cerevo/MKZ4/custom/milkcocoa_javascript/image/b_right.png

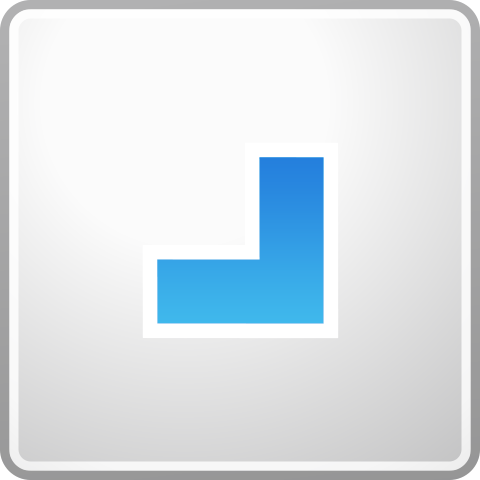
custom/milkcocoa_javascript/image/b_right.png
