cerevo/MKZ4/custom/MKZ4Camera/Pics/Front.jpg

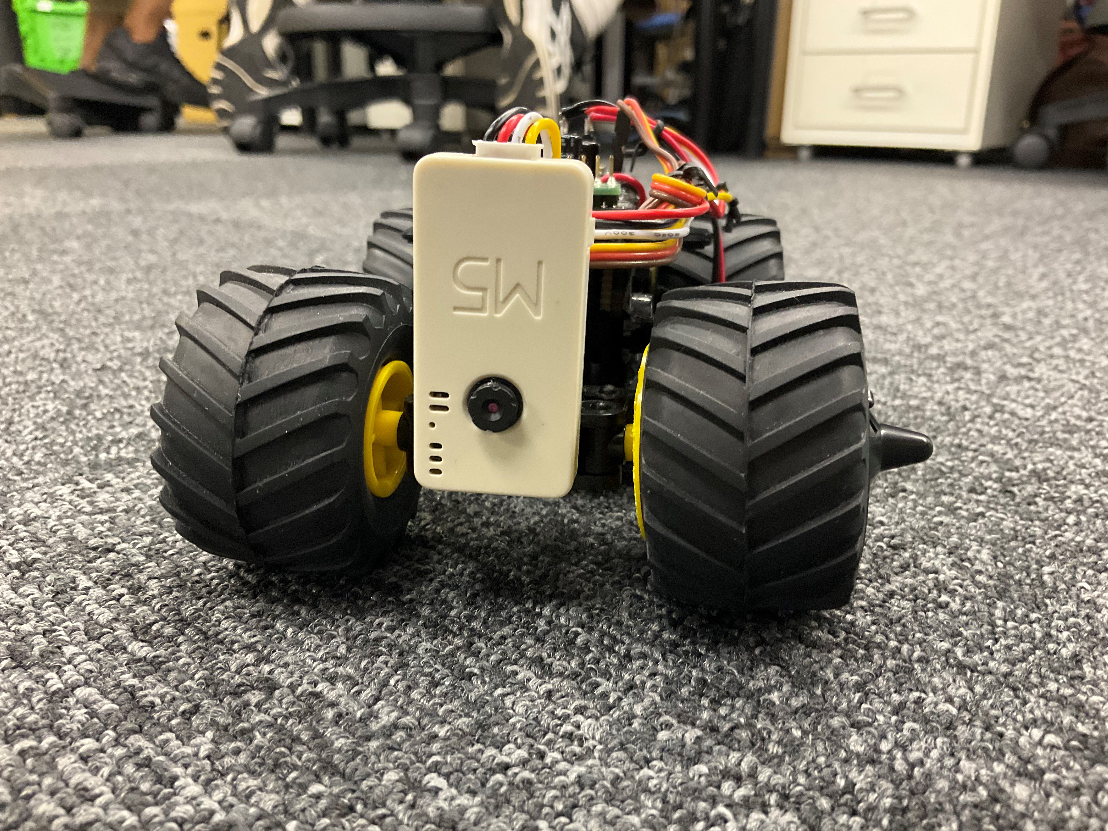
custom/MKZ4Camera/Pics/Front.jpg
