cerevo/MKZ4/custom/MKZ4Camera/CameraWebserver/app_httpd.cpp

// Copyright 2015-2016 Espressif Systems (Shanghai) PTE LTD
//
// Licensed under the Apache License, Version 2.0 (the "License");
// you may not use this file except in compliance with the License.
// You may obtain a copy of the License at
//
//     http://www.apache.org/licenses/LICENSE-2.0
//
// Unless required by applicable law or agreed to in writing, software
// distributed under the License is distributed on an "AS IS" BASIS,
// WITHOUT WARRANTIES OR CONDITIONS OF ANY KIND, either express or implied.
// See the License for the specific language governing permissions and
// limitations under the License.
#include "esp_http_server.h"
#include "esp_timer.h"
#include "esp_camera.h"
#include "img_converters.h"
#include "fb_gfx.h"
#include "driver/ledc.h"
#include "sdkconfig.h"
#include "camera_index.h"

#include "Arduino.h"

#if defined(ARDUINO_ARCH_ESP32) && defined(CONFIG_ARDUHAL_ESP_LOG)
#include "esp32-hal-log.h"
#define TAG "WS"
#else
#include "esp_log.h"
static const char *TAG = "camera_httpd";
#endif

typedef struct
{
    httpd_req_t *req;
    size_t len;
} jpg_chunking_t;

/*
 * Structure holding server handle
 * and internal socket fd in order
 * to use out of request send
 */
struct async_resp_arg
{
    httpd_handle_t hd;
    int fd;
};

#define PART_BOUNDARY "123456789000000000000987654321"
static const char *_STREAM_CONTENT_TYPE = "multipart/x-mixed-replace;boundary=" PART_BOUNDARY;
static const char *_STREAM_BOUNDARY = "\r\n--" PART_BOUNDARY "\r\n";
static const char *_STREAM_PART = "Content-Type: image/jpeg\r\nContent-Length: %u\r\nX-Timestamp: %d.%06d\r\n\r\n";

httpd_handle_t stream_httpd = NULL;
httpd_handle_t camera_httpd = NULL;

typedef struct
{
    size_t size;  //number of values used for filtering
    size_t index; //current value index
    size_t count; //value count
    int sum;
    int *values; //array to be filled with values
} ra_filter_t;

static ra_filter_t ra_filter;

static ra_filter_t *ra_filter_init(ra_filter_t *filter, size_t sample_size)
{
    memset(filter, 0, sizeof(ra_filter_t));

    filter->values = (int *)malloc(sample_size * sizeof(int));
    if (!filter->values)
    {
        return NULL;
    }
    memset(filter->values, 0, sample_size * sizeof(int));

    filter->size = sample_size;
    return filter;
}


///////////////////////////////////////////////////////////////////////////////////////////////////

/*
 * async send function, which we put into the httpd work queue
 */
static void ws_async_send(void *arg)
{
    static const char *data = "Async data";
    struct async_resp_arg *resp_arg = (struct async_resp_arg*)arg;
    httpd_handle_t hd = resp_arg->hd;
    int fd = resp_arg->fd;
    httpd_ws_frame_t ws_pkt;
    memset(&ws_pkt, 0, sizeof(httpd_ws_frame_t));
    ws_pkt.payload = (uint8_t *)data;
    ws_pkt.len = strlen(data);
    ws_pkt.type = HTTPD_WS_TYPE_TEXT;

    httpd_ws_send_frame_async(hd, fd, &ws_pkt);
    free(resp_arg);
}

static esp_err_t trigger_async_send(httpd_handle_t handle, httpd_req_t *req)
{
    struct async_resp_arg *resp_arg = (struct async_resp_arg *)malloc(sizeof(struct async_resp_arg));
    resp_arg->hd = req->handle;
    resp_arg->fd = httpd_req_to_sockfd(req);
    return httpd_queue_work(handle, ws_async_send, resp_arg);
}

/*
 * This handler echos back the received ws data
 * and triggers an async send if certain message received
 */
static esp_err_t echo_handler(httpd_req_t *req)
{
    if (req->method == HTTP_GET)
    {
        ESP_LOGI(TAG, "Handshake done, the new connection was opened");
        return ESP_OK;
    }
    httpd_ws_frame_t ws_pkt;
    uint8_t *buf = NULL;
    memset(&ws_pkt, 0, sizeof(httpd_ws_frame_t));
    ws_pkt.type = HTTPD_WS_TYPE_TEXT;
    /* Set max_len = 0 to get the frame len */
    esp_err_t ret = httpd_ws_recv_frame(req, &ws_pkt, 0);
    if (ret != ESP_OK)
    {
        ESP_LOGE(TAG, "httpd_ws_recv_frame failed to get frame len with %d", ret);
        return ret;
    }
    ESP_LOGI(TAG, "frame len is %d", ws_pkt.len);
    if (ws_pkt.len)
    {
        /* ws_pkt.len + 1 is for NULL termination as we are expecting a string */
        buf = (uint8_t*)calloc(1, ws_pkt.len + 1);
        if (buf == NULL)
        {
            ESP_LOGE(TAG, "Failed to calloc memory for buf");
            return ESP_ERR_NO_MEM;
        }
        ws_pkt.payload = buf;
        /* Set max_len = ws_pkt.len to get the frame payload */
        ret = httpd_ws_recv_frame(req, &ws_pkt, ws_pkt.len);
        if (ret != ESP_OK)
        {
            ESP_LOGE(TAG, "httpd_ws_recv_frame failed with %d", ret);
            free(buf);
            return ret;
        }
        ESP_LOGI(TAG, "Got packet with message: %s", ws_pkt.payload);
        // ESP_LOGE(TAG, "capture called %s\n", ws_pkt.payload);
        Serial2.printf("A%s\n", ws_pkt.payload);
    }
    ESP_LOGI(TAG, "Packet type: %d", ws_pkt.type);
    if (ws_pkt.type == HTTPD_WS_TYPE_TEXT &&
        strcmp((char *)ws_pkt.payload, "Trigger async") == 0)
    {
        free(buf);
        return trigger_async_send(req->handle, req);
    }

    ret = httpd_ws_send_frame(req, &ws_pkt);
    if (ret != ESP_OK)
    {
        ESP_LOGE(TAG, "httpd_ws_send_frame failed with %d", ret);
    }
    free(buf);
    return ret;
}

static esp_err_t move_handler(httpd_req_t *req)
{
    ESP_LOGE(TAG, "capture called %s\n", req->uri);
    char *coordinate = strstr(req->uri, "?_cb=") + 5;
    Serial2.printf("%s\n", coordinate);

    httpd_resp_set_hdr(req, "Access-Control-Allow-Origin", "*");
    return httpd_resp_send(req, NULL, 0);
}

///////////////////////////////////////////////////////////////////////////////////////////////////

static size_t jpg_encode_stream(void *arg, size_t index, const void *data, size_t len)
{
    jpg_chunking_t *j = (jpg_chunking_t *)arg;
    if (!index)
    {
        j->len = 0;
    }
    if (httpd_resp_send_chunk(j->req, (const char *)data, len) != ESP_OK)
    {
        return 0;
    }
    j->len += len;
    return len;
}

static esp_err_t stream_handler(httpd_req_t *req)
{
    camera_fb_t *fb = NULL;
    struct timeval _timestamp;
    esp_err_t res = ESP_OK;
    size_t _jpg_buf_len = 0;
    uint8_t *_jpg_buf = NULL;
    char *part_buf[128];

    static int64_t last_frame = 0;
    if (!last_frame)
    {
        last_frame = esp_timer_get_time();
    }

    res = httpd_resp_set_type(req, _STREAM_CONTENT_TYPE);
    if (res != ESP_OK)
    {
        return res;
    }

    httpd_resp_set_hdr(req, "Access-Control-Allow-Origin", "*");
    httpd_resp_set_hdr(req, "X-Framerate", "60");

    while (true)
    {
        fb = esp_camera_fb_get();
        if (!fb)
        {
            ESP_LOGE(TAG, "Camera capture failed");
            res = ESP_FAIL;
        }
        else
        {
            _timestamp.tv_sec = fb->timestamp.tv_sec;
            _timestamp.tv_usec = fb->timestamp.tv_usec;

                if (fb->format != PIXFORMAT_JPEG)
                {
                    bool jpeg_converted = frame2jpg(fb, 80, &_jpg_buf, &_jpg_buf_len);
                    esp_camera_fb_return(fb);
                    fb = NULL;
                    if (!jpeg_converted)
                    {
                        ESP_LOGE(TAG, "JPEG compression failed");
                        res = ESP_FAIL;
                    }
                }
                else
                {
                    _jpg_buf_len = fb->len;
                    _jpg_buf = fb->buf;
                }
        }
        if (res == ESP_OK)
        {
            res = httpd_resp_send_chunk(req, _STREAM_BOUNDARY, strlen(_STREAM_BOUNDARY));
        }
        if (res == ESP_OK)
        {
            size_t hlen = snprintf((char *)part_buf, 128, _STREAM_PART, _jpg_buf_len, _timestamp.tv_sec, _timestamp.tv_usec);
            res = httpd_resp_send_chunk(req, (const char *)part_buf, hlen);
        }
        if (res == ESP_OK)
        {
            res = httpd_resp_send_chunk(req, (const char *)_jpg_buf, _jpg_buf_len);
        }
        if (fb)
        {
            esp_camera_fb_return(fb);
            fb = NULL;
            _jpg_buf = NULL;
        }
        else if (_jpg_buf)
        {
            free(_jpg_buf);
            _jpg_buf = NULL;
        }
        if (res != ESP_OK)
        {
            ESP_LOGE(TAG, "send frame failed failed");
            break;
        }
        int64_t fr_end = esp_timer_get_time();

        int64_t frame_time = fr_end - last_frame;
        frame_time /= 1000;

        ESP_LOGI(TAG, "MJPG: %uB %ums (%.1ffps), AVG: %ums (%.1ffps)", (uint32_t)(_jpg_buf_len), (uint32_t)frame_time, 1000.0 / (uint32_t)frame_time, avg_frame_time, 1000.0 / avg_frame_time);
    }

    return res;
}

static esp_err_t parse_get(httpd_req_t *req, char **obuf)
{
    char *buf = NULL;
    size_t buf_len = 0;

    buf_len = httpd_req_get_url_query_len(req) + 1;
    if (buf_len > 1) {
        buf = (char *)malloc(buf_len);
        if (!buf) {
            httpd_resp_send_500(req);
            return ESP_FAIL;
        }
        if (httpd_req_get_url_query_str(req, buf, buf_len) == ESP_OK) {
            *obuf = buf;
            return ESP_OK;
        }
        free(buf);
    }
    httpd_resp_send_404(req);
    return ESP_FAIL;
}

static esp_err_t cmd_handler(httpd_req_t *req)
{
    char *buf = NULL;
    char variable[32];
    char value[32];

    if (parse_get(req, &buf) != ESP_OK) {
        return ESP_FAIL;
    }
    if (httpd_query_key_value(buf, "var", variable, sizeof(variable)) != ESP_OK ||
        httpd_query_key_value(buf, "val", value, sizeof(value)) != ESP_OK) {
        free(buf);
        httpd_resp_send_404(req);
        return ESP_FAIL;
    }
    free(buf);

    int val = atoi(value);
    ESP_LOGI(TAG, "%s = %d", variable, val);
    sensor_t *s = esp_camera_sensor_get();
    int res = 0;

    if (!strcmp(variable, "framesize")) {
        if (s->pixformat == PIXFORMAT_JPEG) {
            res = s->set_framesize(s, (framesize_t)val);
        }
    }
    else if (!strcmp(variable, "quality"))
        res = s->set_quality(s, val);
    else if (!strcmp(variable, "contrast"))
        res = s->set_contrast(s, val);
    else if (!strcmp(variable, "brightness"))
        res = s->set_brightness(s, val);
    else if (!strcmp(variable, "saturation"))
        res = s->set_saturation(s, val);
    else if (!strcmp(variable, "gainceiling"))
        res = s->set_gainceiling(s, (gainceiling_t)val);
    else if (!strcmp(variable, "colorbar"))
        res = s->set_colorbar(s, val);
    else if (!strcmp(variable, "awb"))
        res = s->set_whitebal(s, val);
    else if (!strcmp(variable, "agc"))
        res = s->set_gain_ctrl(s, val);
    else if (!strcmp(variable, "aec"))
        res = s->set_exposure_ctrl(s, val);
    else if (!strcmp(variable, "hmirror"))
        res = s->set_hmirror(s, val);
    else if (!strcmp(variable, "vflip"))
        res = s->set_vflip(s, val);
    else if (!strcmp(variable, "awb_gain"))
        res = s->set_awb_gain(s, val);
    else if (!strcmp(variable, "agc_gain"))
        res = s->set_agc_gain(s, val);
    else if (!strcmp(variable, "aec_value"))
        res = s->set_aec_value(s, val);
    else if (!strcmp(variable, "aec2"))
        res = s->set_aec2(s, val);
    else if (!strcmp(variable, "dcw"))
        res = s->set_dcw(s, val);
    else if (!strcmp(variable, "bpc"))
        res = s->set_bpc(s, val);
    else if (!strcmp(variable, "wpc"))
        res = s->set_wpc(s, val);
    else if (!strcmp(variable, "raw_gma"))
        res = s->set_raw_gma(s, val);
    else if (!strcmp(variable, "lenc"))
        res = s->set_lenc(s, val);
    else if (!strcmp(variable, "special_effect"))
        res = s->set_special_effect(s, val);
    else if (!strcmp(variable, "wb_mode"))
        res = s->set_wb_mode(s, val);
    else if (!strcmp(variable, "ae_level"))
        res = s->set_ae_level(s, val);

    else {
        ESP_LOGI(TAG, "Unknown command: %s", variable);
        res = -1;
    }

    if (res < 0) {
        return httpd_resp_send_500(req);
    }

    httpd_resp_set_hdr(req, "Access-Control-Allow-Origin", "*");
    return httpd_resp_send(req, NULL, 0);
}

static int print_reg(char * p, sensor_t * s, uint16_t reg, uint32_t mask){
    return sprintf(p, "\"0x%x\":%u,", reg, s->get_reg(s, reg, mask));
}

static esp_err_t status_handler(httpd_req_t *req)
{
    static char json_response[1024];

    sensor_t *s = esp_camera_sensor_get();
    char *p = json_response;
    *p++ = '{';

    if(s->id.PID == OV5640_PID || s->id.PID == OV3660_PID){
        for(int reg = 0x3400; reg < 0x3406; reg+=2){
            p+=print_reg(p, s, reg, 0xFFF);//12 bit
        }
        p+=print_reg(p, s, 0x3406, 0xFF);

        p+=print_reg(p, s, 0x3500, 0xFFFF0);//16 bit
        p+=print_reg(p, s, 0x3503, 0xFF);
        p+=print_reg(p, s, 0x350a, 0x3FF);//10 bit
        p+=print_reg(p, s, 0x350c, 0xFFFF);//16 bit

        for(int reg = 0x5480; reg <= 0x5490; reg++){
            p+=print_reg(p, s, reg, 0xFF);
        }

        for(int reg = 0x5380; reg <= 0x538b; reg++){
            p+=print_reg(p, s, reg, 0xFF);
        }

        for(int reg = 0x5580; reg < 0x558a; reg++){
            p+=print_reg(p, s, reg, 0xFF);
        }
        p+=print_reg(p, s, 0x558a, 0x1FF);//9 bit
    } else if(s->id.PID == OV2640_PID){
        p+=print_reg(p, s, 0xd3, 0xFF);
        p+=print_reg(p, s, 0x111, 0xFF);
        p+=print_reg(p, s, 0x132, 0xFF);
    }

    p += sprintf(p, "\"xclk\":%u,", s->xclk_freq_hz / 1000000);
    p += sprintf(p, "\"pixformat\":%u,", s->pixformat);
    p += sprintf(p, "\"framesize\":%u,", s->status.framesize);
    p += sprintf(p, "\"quality\":%u,", s->status.quality);
    p += sprintf(p, "\"brightness\":%d,", s->status.brightness);
    p += sprintf(p, "\"contrast\":%d,", s->status.contrast);
    p += sprintf(p, "\"saturation\":%d,", s->status.saturation);
    p += sprintf(p, "\"sharpness\":%d,", s->status.sharpness);
    p += sprintf(p, "\"special_effect\":%u,", s->status.special_effect);
    p += sprintf(p, "\"wb_mode\":%u,", s->status.wb_mode);
    p += sprintf(p, "\"awb\":%u,", s->status.awb);
    p += sprintf(p, "\"awb_gain\":%u,", s->status.awb_gain);
    p += sprintf(p, "\"aec\":%u,", s->status.aec);
    p += sprintf(p, "\"aec2\":%u,", s->status.aec2);
    p += sprintf(p, "\"ae_level\":%d,", s->status.ae_level);
    p += sprintf(p, "\"aec_value\":%u,", s->status.aec_value);
    p += sprintf(p, "\"agc\":%u,", s->status.agc);
    p += sprintf(p, "\"agc_gain\":%u,", s->status.agc_gain);
    p += sprintf(p, "\"gainceiling\":%u,", s->status.gainceiling);
    p += sprintf(p, "\"bpc\":%u,", s->status.bpc);
    p += sprintf(p, "\"wpc\":%u,", s->status.wpc);
    p += sprintf(p, "\"raw_gma\":%u,", s->status.raw_gma);
    p += sprintf(p, "\"lenc\":%u,", s->status.lenc);
    p += sprintf(p, "\"hmirror\":%u,", s->status.hmirror);
    p += sprintf(p, "\"dcw\":%u,", s->status.dcw);
    p += sprintf(p, "\"colorbar\":%u", s->status.colorbar);
    p += sprintf(p, ",\"led_intensity\":%d", -1);
    *p++ = '}';
    *p++ = 0;
    httpd_resp_set_type(req, "application/json");
    httpd_resp_set_hdr(req, "Access-Control-Allow-Origin", "*");
    return httpd_resp_send(req, json_response, strlen(json_response));
}

static int parse_get_var(char *buf, const char * key, int def)
{
    char _int[16];
    if(httpd_query_key_value(buf, key, _int, sizeof(_int)) != ESP_OK){
        return def;
    }
    return atoi(_int);
}

static esp_err_t win_handler(httpd_req_t *req)
{
    char *buf = NULL;

    if (parse_get(req, &buf) != ESP_OK) {
        return ESP_FAIL;
    }

    int startX = parse_get_var(buf, "sx", 0);
    int startY = parse_get_var(buf, "sy", 0);
    int endX = parse_get_var(buf, "ex", 0);
    int endY = parse_get_var(buf, "ey", 0);
    int offsetX = parse_get_var(buf, "offx", 0);
    int offsetY = parse_get_var(buf, "offy", 0);
    int totalX = parse_get_var(buf, "tx", 0);
    int totalY = parse_get_var(buf, "ty", 0);
    int outputX = parse_get_var(buf, "ox", 0);
    int outputY = parse_get_var(buf, "oy", 0);
    bool scale = parse_get_var(buf, "scale", 0) == 1;
    bool binning = parse_get_var(buf, "binning", 0) == 1;
    free(buf);

    ESP_LOGI(TAG, "Set Window: Start: %d %d, End: %d %d, Offset: %d %d, Total: %d %d, Output: %d %d, Scale: %u, Binning: %u", startX, startY, endX, endY, offsetX, offsetY, totalX, totalY, outputX, outputY, scale, binning);
    sensor_t *s = esp_camera_sensor_get();
    int res = s->set_res_raw(s, startX, startY, endX, endY, offsetX, offsetY, totalX, totalY, outputX, outputY, scale, binning);
    if (res) {
        return httpd_resp_send_500(req);
    }

    httpd_resp_set_hdr(req, "Access-Control-Allow-Origin", "*");
    return httpd_resp_send(req, NULL, 0);
}

static esp_err_t index_handler(httpd_req_t *req)
{
    httpd_resp_set_type(req, "text/html");
    sensor_t *s = esp_camera_sensor_get();
    if (s != NULL) {
        return httpd_resp_send(req, index_ov2640_html, strlen(index_ov2640_html));
    } else {
        ESP_LOGE(TAG, "Camera sensor not found");
        return httpd_resp_send_500(req);
    }
}

void startCameraServer()
{
    httpd_config_t config = HTTPD_DEFAULT_CONFIG();
    config.max_uri_handlers = 16;

    httpd_uri_t index_uri = {
        .uri = "/",
        .method = HTTP_GET,
        .handler = index_handler,
        .user_ctx = NULL};

    httpd_uri_t status_uri = {
        .uri = "/status",
        .method = HTTP_GET,
        .handler = status_handler,
        .user_ctx = NULL};

    httpd_uri_t cmd_uri = {
        .uri = "/control",
        .method = HTTP_GET,
        .handler = cmd_handler,
        .user_ctx = NULL};

    httpd_uri_t stream_uri = {
        .uri = "/stream",
        .method = HTTP_GET,
        .handler = stream_handler,
        .user_ctx = NULL};

    httpd_uri_t win_uri = {
        .uri = "/resolution",
        .method = HTTP_GET,
        .handler = win_handler,
        .user_ctx = NULL};

    httpd_uri_t ws = {
        .uri = "/ws",
        .method = HTTP_GET,
        .handler = echo_handler,
        .user_ctx = NULL,
        .is_websocket = true};

    httpd_uri_t move_uri = {
        .uri = "/move",
        .method = HTTP_GET,
        .handler = move_handler,
        .user_ctx = NULL};

    ra_filter_init(&ra_filter, 20);

    ESP_LOGI(TAG, "Starting web server on port: '%d'", config.server_port);
    if (httpd_start(&camera_httpd, &config) == ESP_OK)
    {
        httpd_register_uri_handler(camera_httpd, &index_uri);
        httpd_register_uri_handler(camera_httpd, &cmd_uri);
        httpd_register_uri_handler(camera_httpd, &status_uri);

        httpd_register_uri_handler(camera_httpd, &win_uri);

        httpd_register_uri_handler(camera_httpd, &ws);
        httpd_register_uri_handler(camera_httpd, &move_uri);
    }

    config.server_port += 1;
    config.ctrl_port += 1;
    ESP_LOGI(TAG, "Starting stream server on port: '%d'", config.server_port);
    if (httpd_start(&stream_httpd, &config) == ESP_OK)
    {
        httpd_register_uri_handler(stream_httpd, &stream_uri);
    }
}
